yeokm1/graphics-gremlin-hdmi/images/gg-hdmi-board-prog-pin-front.jpg

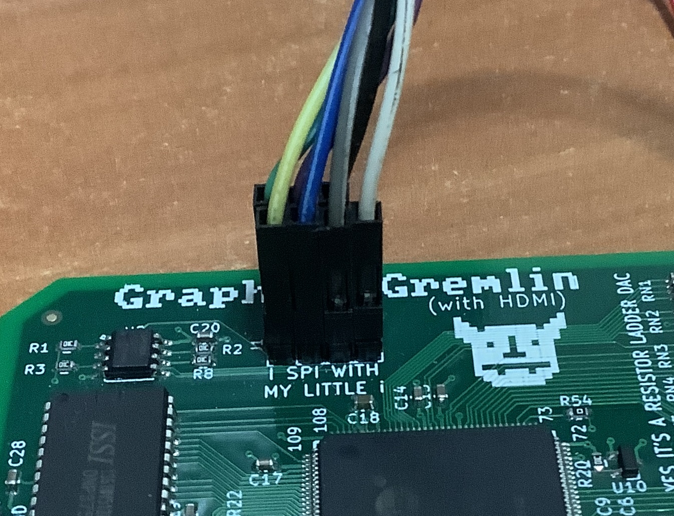
images/gg-hdmi-board-prog-pin-front.jpg
