yeokm1/graphics-gremlin-hdmi/images/gg-hdmi-board-side-bracket.jpg

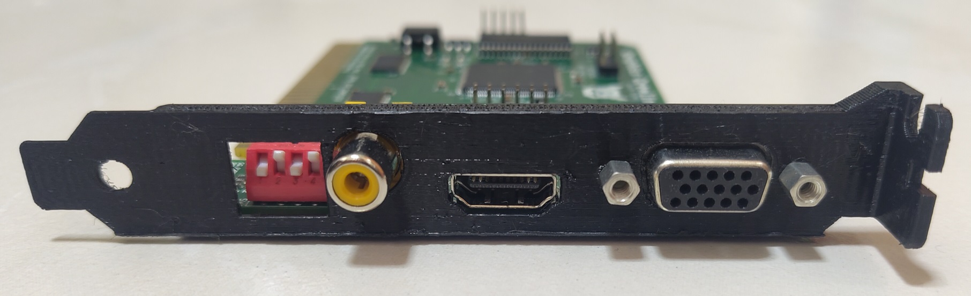
images/gg-hdmi-board-side-bracket.jpg
