yeokm1/graphics-gremlin-hdmi/images/gg-hdmi-ft2232h-diagram.png

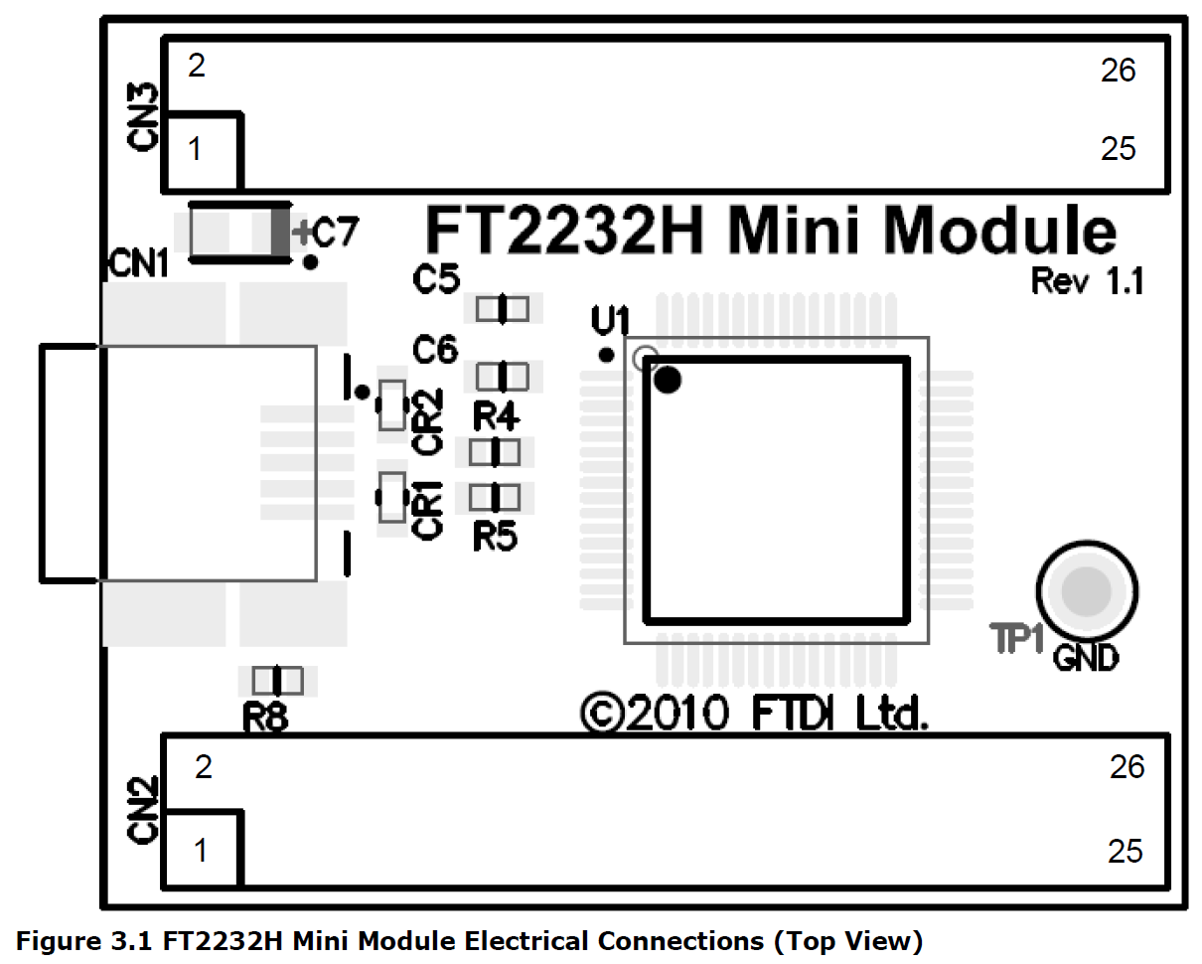
images/gg-hdmi-ft2232h-diagram.png
