yeokm1/graphics-gremlin-hdmi/images/gg-hdmi-prog-1.jpg

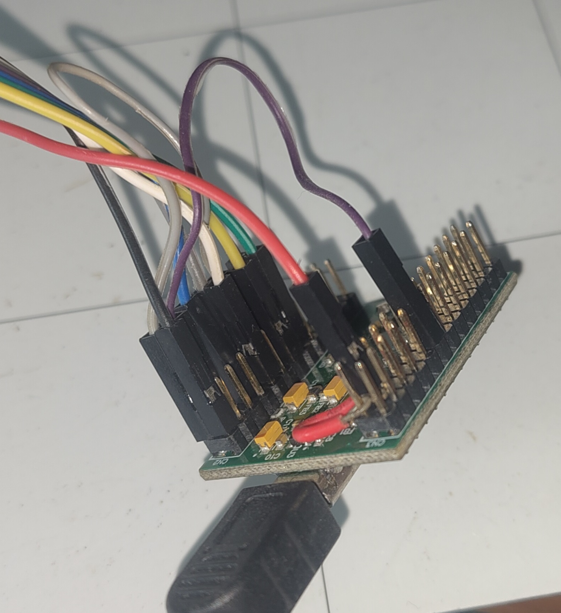
images/gg-hdmi-prog-1.jpg
