yeokm1/graphics-gremlin-hdmi/images/gg-hdmi-prog-2.jpg

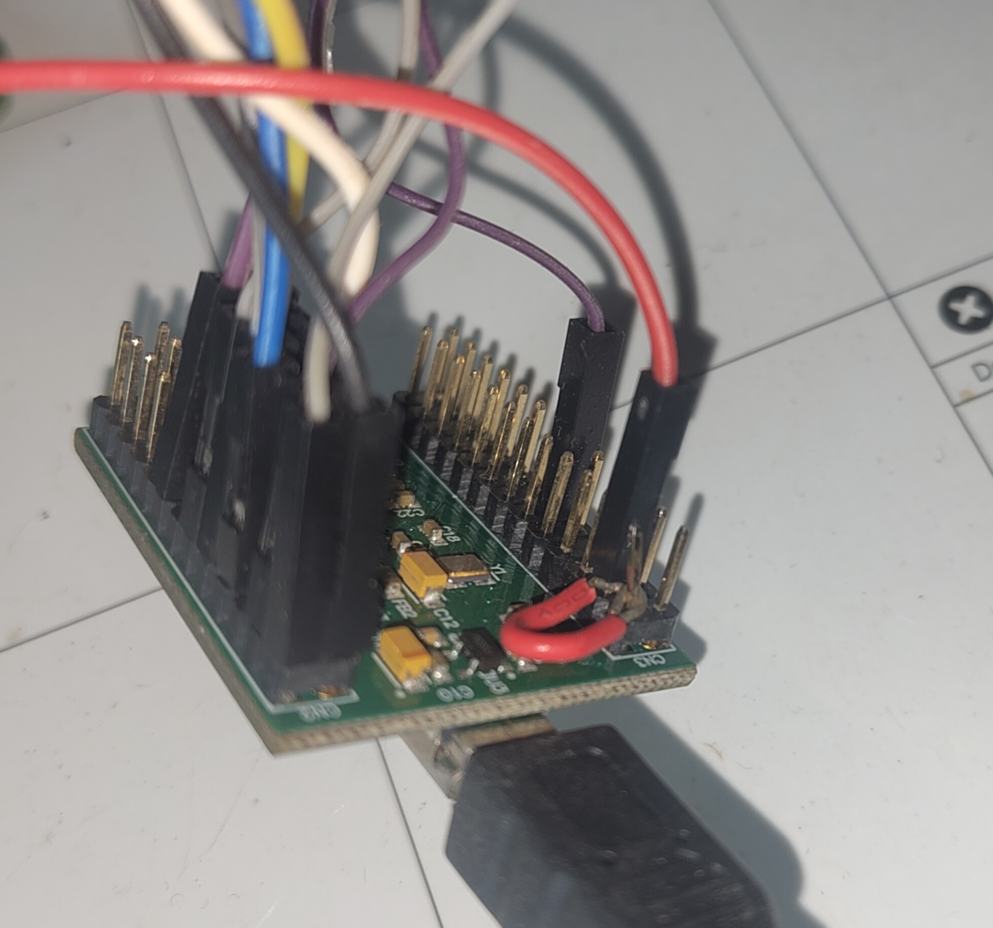
images/gg-hdmi-prog-2.jpg
