yeokm1/graphics-gremlin-hdmi/images/gg-hdmi-prog-pin-connected.jpg

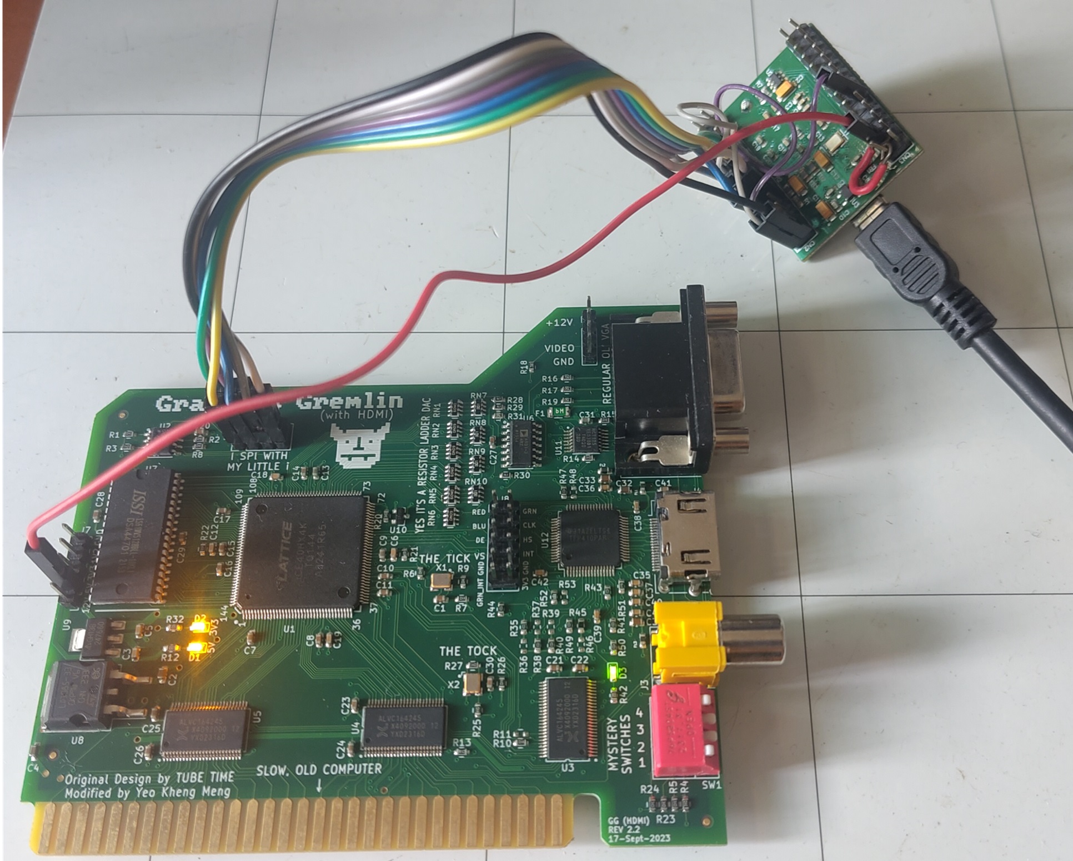
images/gg-hdmi-prog-pin-connected.jpg
