yeokm1/graphics-gremlin-hdmi/images/gg-hdmi-zadig0.png

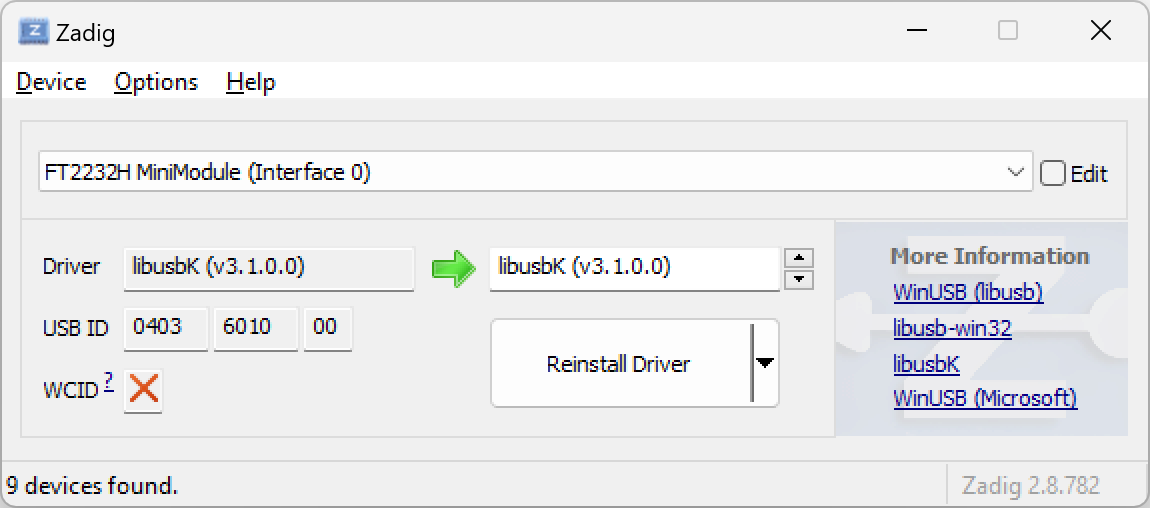
images/gg-hdmi-zadig0.png
