yeokm1/graphics-gremlin-hdmi/images/gg-hdmi-test-cga70-hdmi-big.jpg

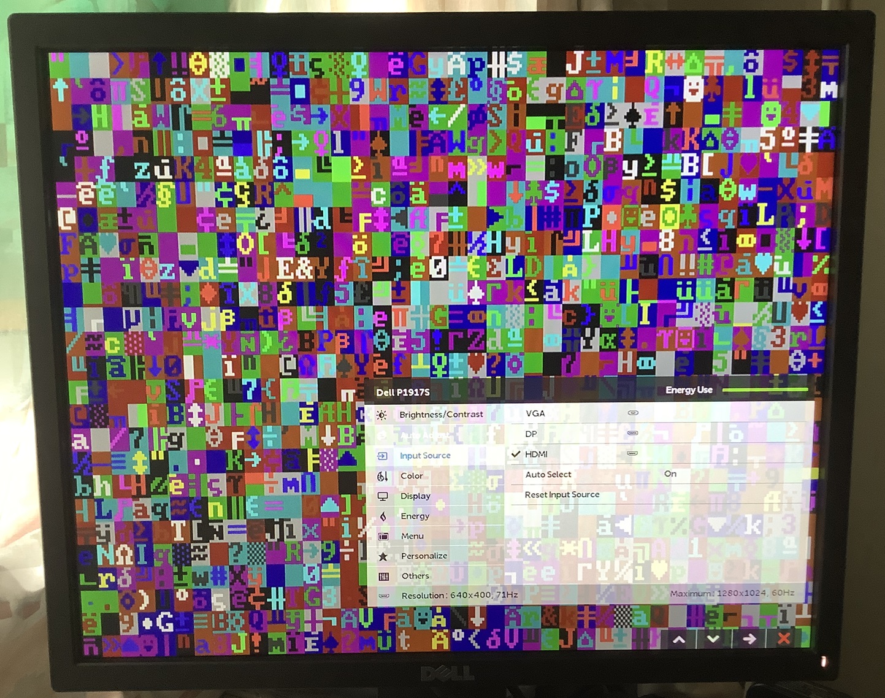
images/gg-hdmi-test-cga70-hdmi-big.jpg
