yeokm1/graphics-gremlin-hdmi/images/gg-hdmi-test-cga-normal.jpg

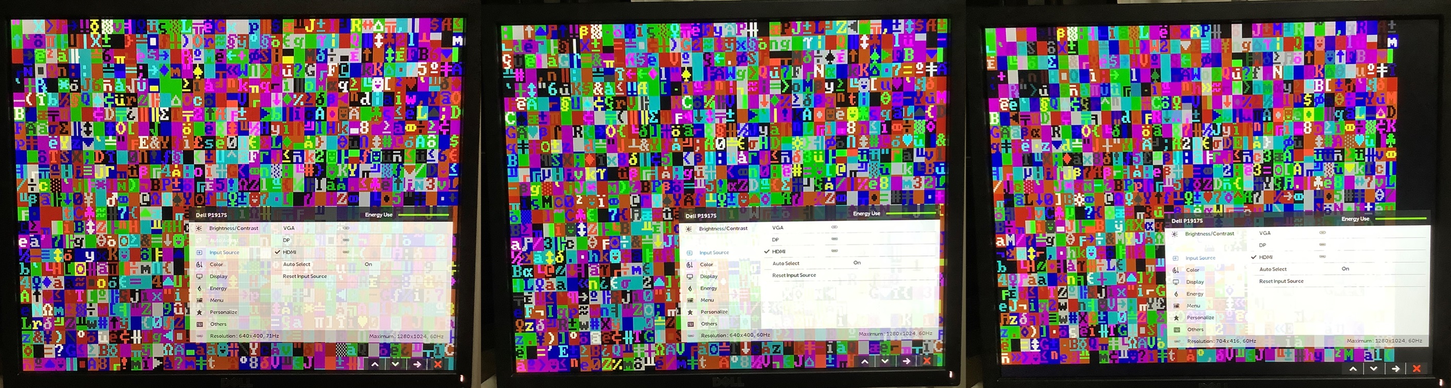
images/gg-hdmi-test-cga-normal.jpg
