yeokm1/graphics-gremlin-hdmi/images/gg-hdmi-test-cga-thin.jpg

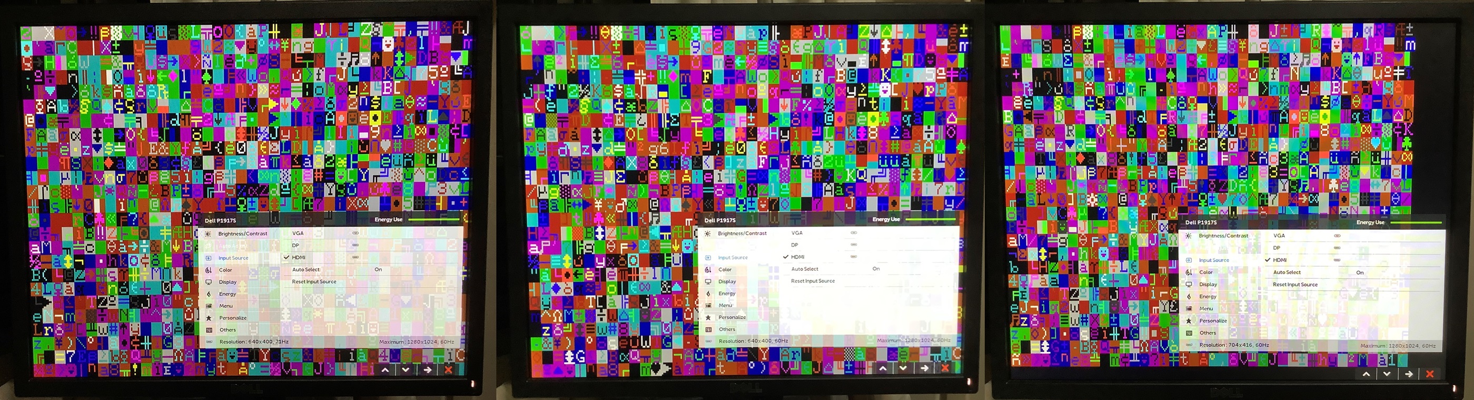
images/gg-hdmi-test-cga-thin.jpg
