yeokm1/graphics-gremlin-hdmi/images/gg-hdmi-test-mda-hdmi-colours.jpg

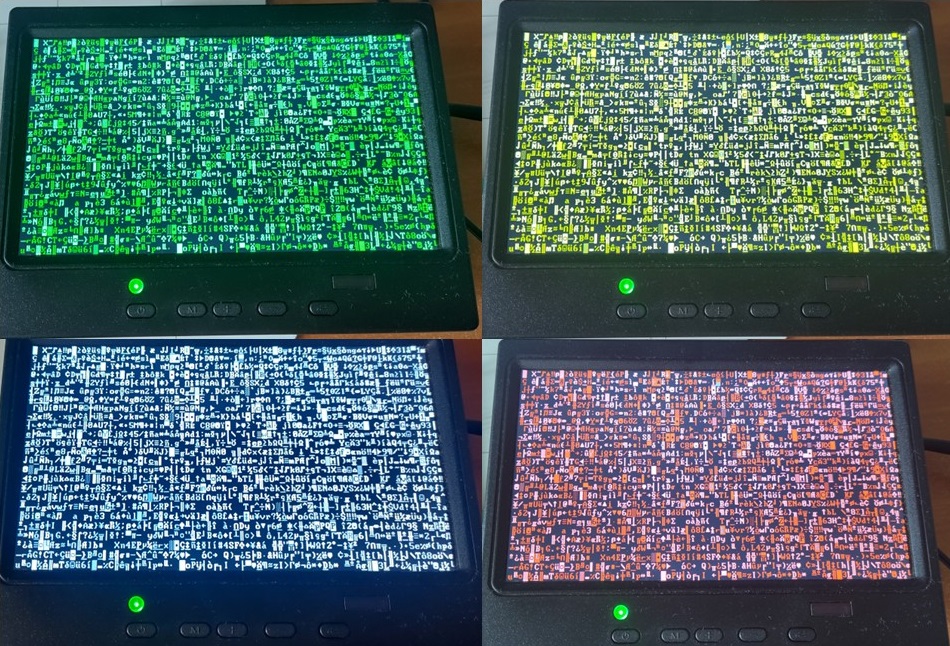
images/gg-hdmi-test-mda-hdmi-colours.jpg
