yeokm1/graphics-gremlin-hdmi/images/gg-hdmi-test-mda-hdmi-green.jpg

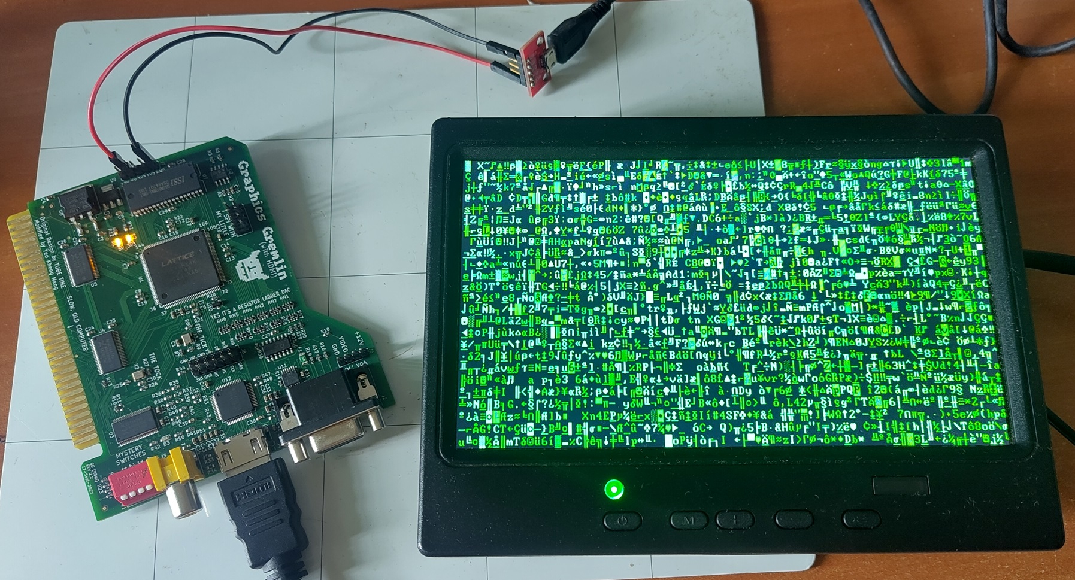
images/gg-hdmi-test-mda-hdmi-green.jpg
