yeokm1/graphics-gremlin-hdmi/images/gg-hdmi-test-mda-vga.jpg

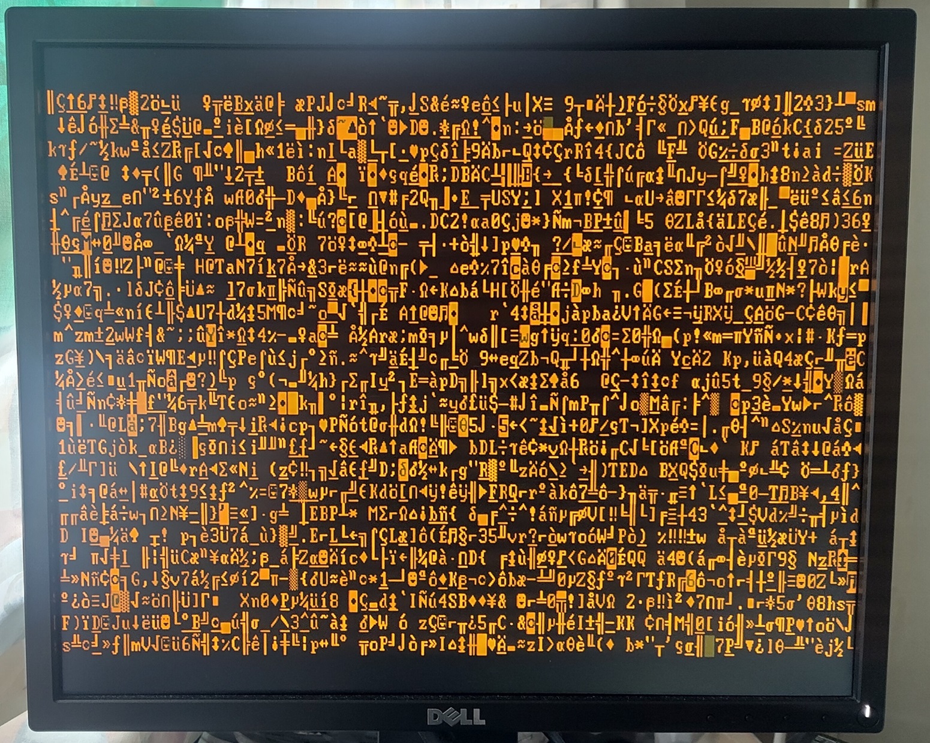
images/gg-hdmi-test-mda-vga.jpg
